SP5GW/Ham_Transceiver_Power_Supply/img/front_2.jpg

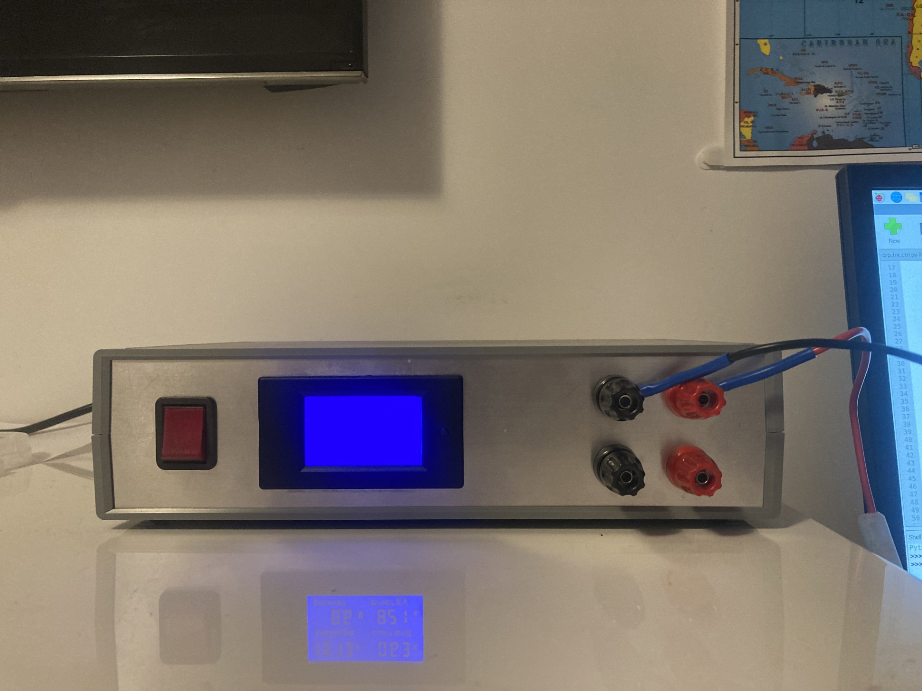
img/front_2.jpg
