SP5GW/Ham_Transceiver_Power_Supply/docs/Integration_Diagram_Ham_Transceiver_Power_Supply.kicad_sch

## KiCad design docs/Integration_Diagram_Ham_Transceiver_Power_Supply.kicad_sch (2024-01-28)

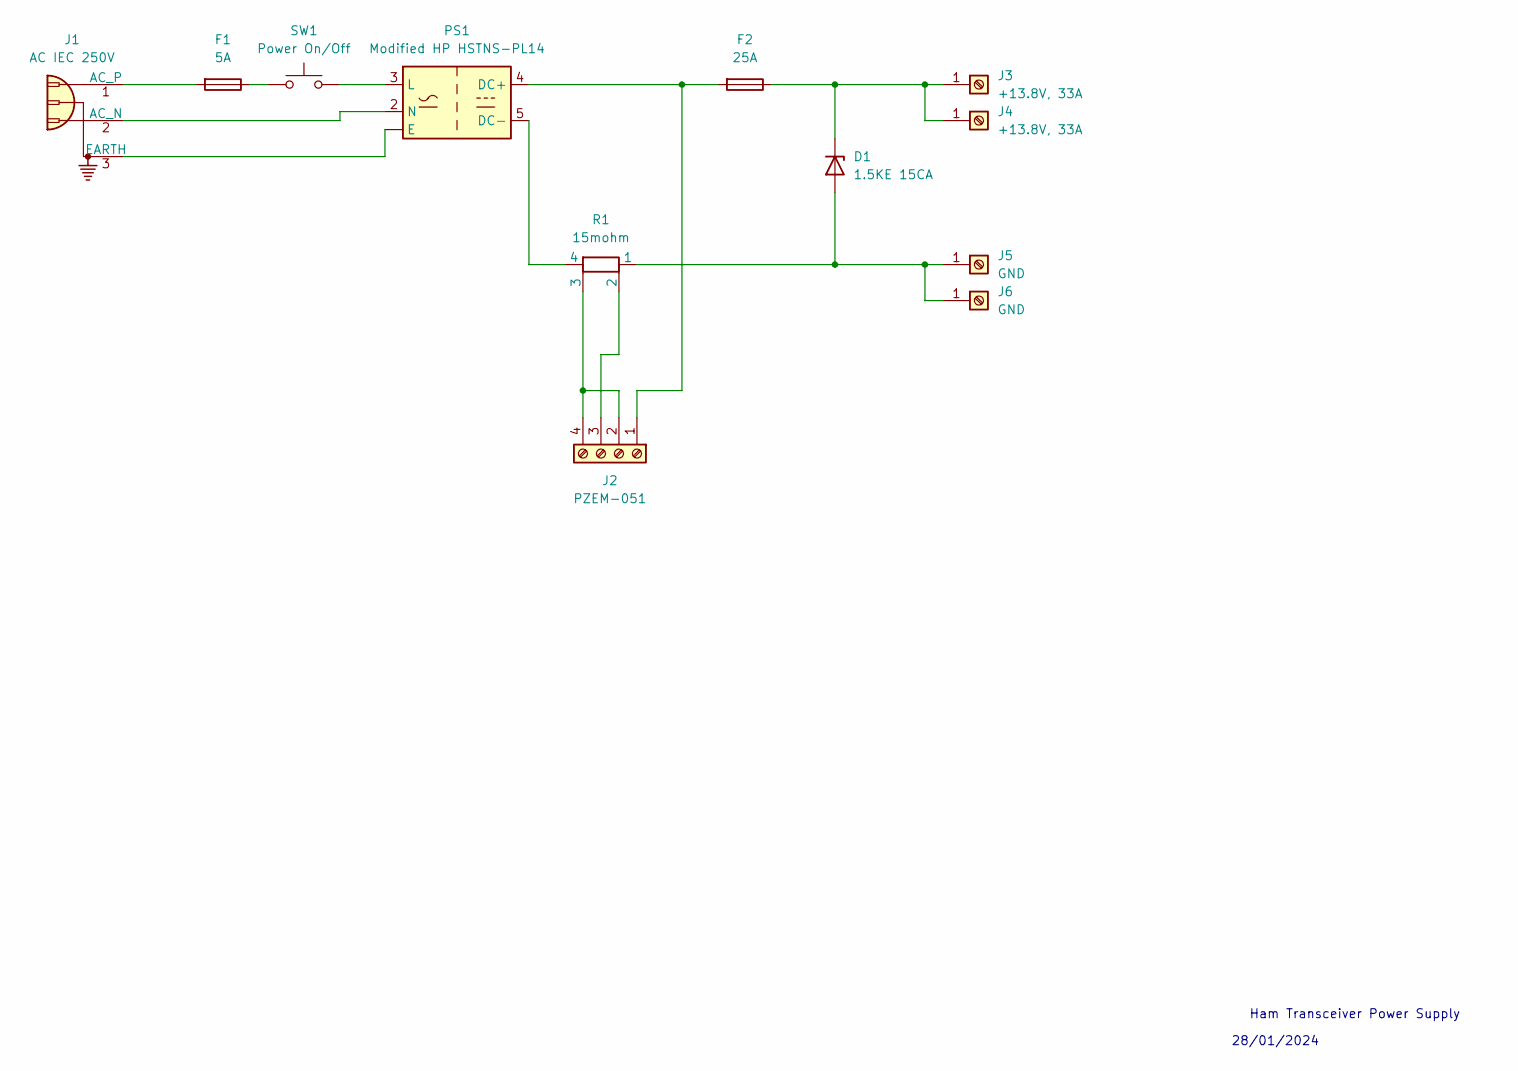
[picture p15: schematic Integration_Diagram_Ham_Transceiver_Power_Supply.kicad_sch]

Parts:
D1: 1.5KE 15CA
F1: 5A
F2: 25A
J1: AC IEC 250V
J2: PZEM-051
J3, J4: +13.8V, 33A
J5, J6: GND
PS1: Modified HP HSTNS-PL14; Converter_ACDC_Vigortronix_VTX-214-015-1xx_THT
R1: 15mohm
SW1: Power On/Off

Connections:
unnamed: D1.1 (K), F2.1, J3.1, J4.1
unnamed: D1.2 (A), J5.1, J6.1, R1.1
unnamed: F1.1, SW1.1
unnamed: F1.2, J1.1 (AC_P)
unnamed: F2.2, J2.1, PS1.4 (DC+)
unnamed: J1.2 (AC_N), PS1.2 (N)
unnamed: J1.3 (EARTH), PS1. (E)
unnamed: J2.2, J2.4, R1.3
unnamed: J2.3, R1.2
unnamed: PS1.3 (L), SW1.2
unnamed: PS1.5 (DC-), R1.4

Notes on the sheet:
Ham Transceiver Power Supply
28/01/2024
